alimleahat/analog-audio-visualizer-pcb/docs/validation/original-drc.png

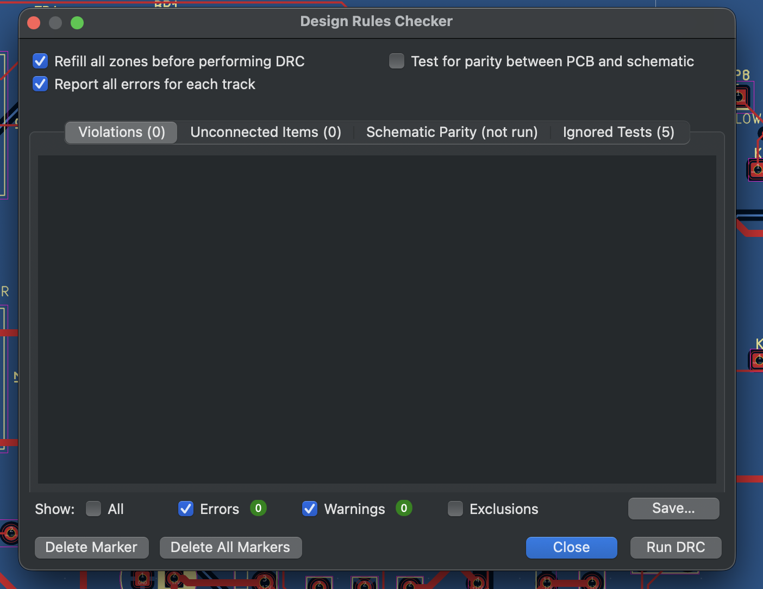
docs/validation/original-drc.png
