alimleahat/analog-audio-visualizer-pcb/docs/validation/original-erc.png

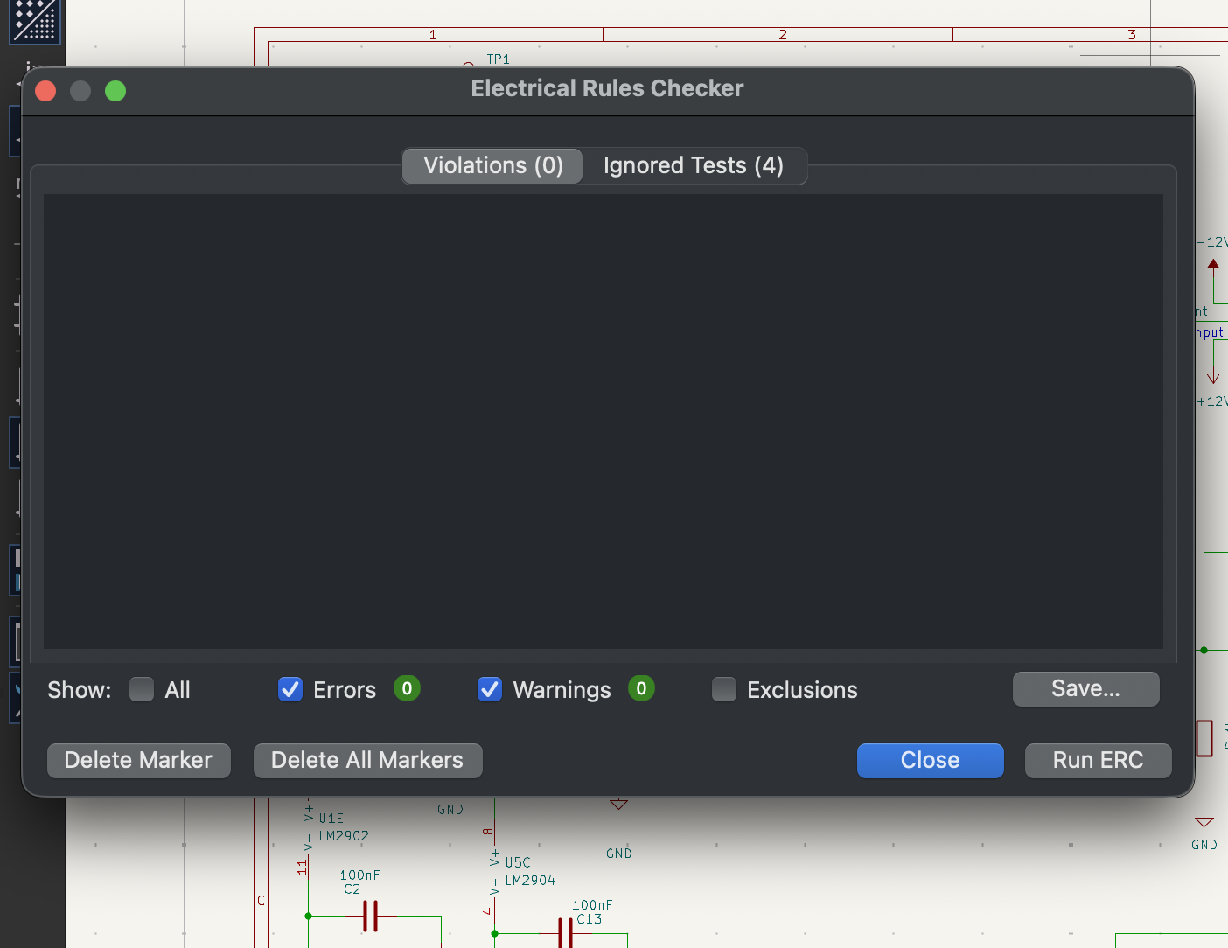
docs/validation/original-erc.png
